Azgar901/BE_POO_KTANE/3D File/Module Timer/Erreur/Couvercle_Timer3.3mf

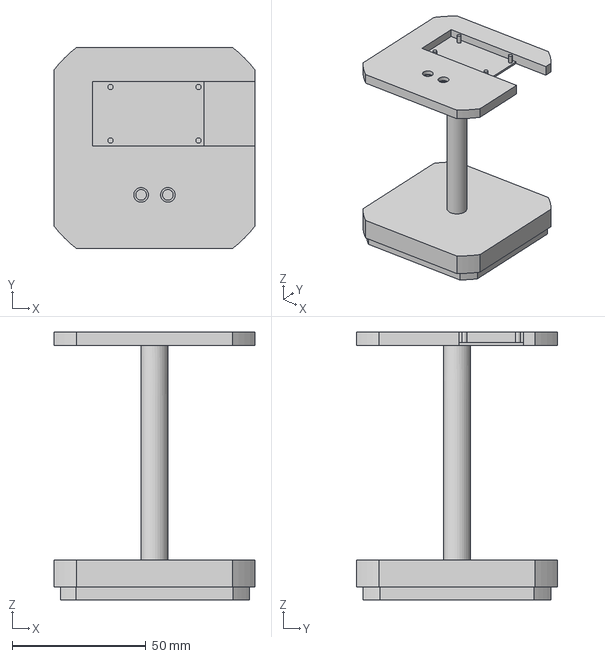
[picture p23: CAD file, 2026-01-14]
3D File/Module Timer/Erreur/Couvercle_Timer3.3mf
75.0 x 75.0 x 100.0 mm
