Azgar901/BE_POO_KTANE/3D File/Casier Modulable/Erreur/Drawer_CasingV5.3mf

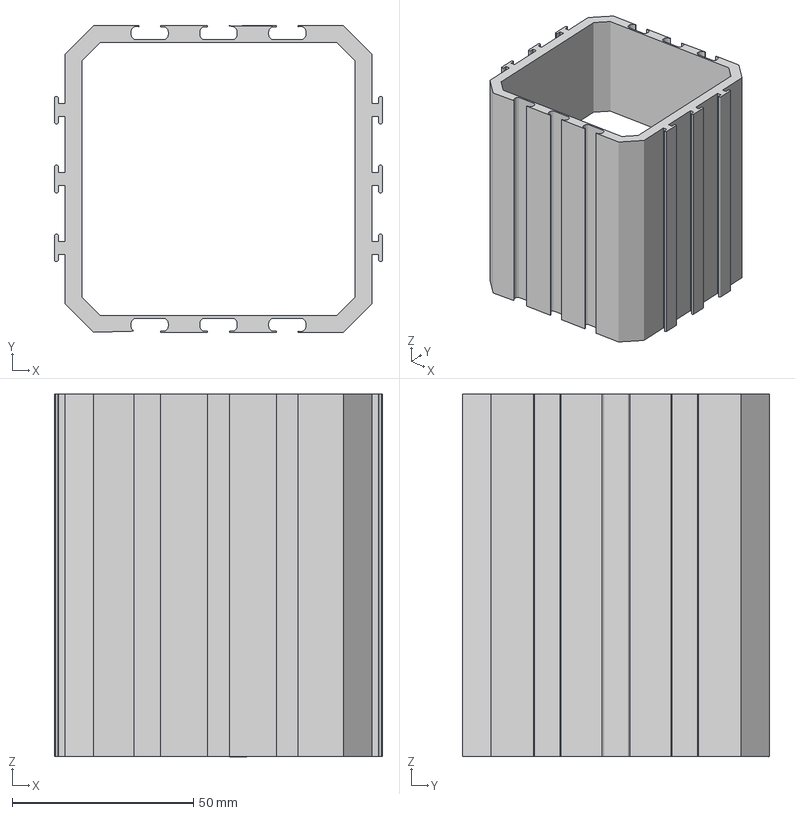
[picture p24: CAD file, 2026-01-14]
3D File/Casier Modulable/Erreur/Drawer_CasingV5.3mf
90.6 x 84.6 x 100.2 mm
