Azgar901/BE_POO_KTANE/3D File/Module LCD/Erreur/LCD_CasingV1.3mf

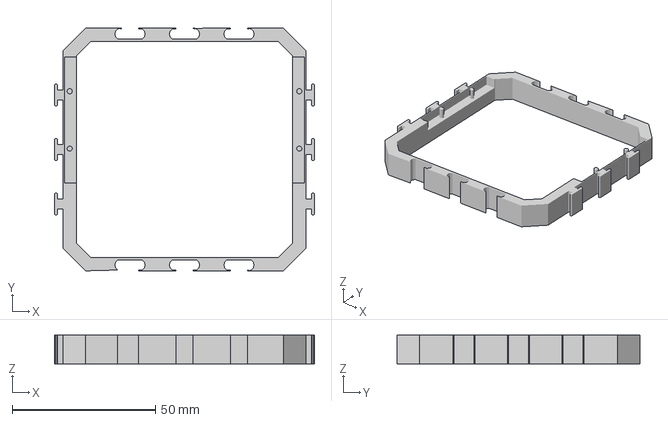
[picture p25: CAD file, 2026-01-14]
3D File/Module LCD/Erreur/LCD_CasingV1.3mf
90.6 x 84.6 x 10.0 mm
