Azgar901/BE_POO_KTANE/3D File/Module Simon/Modelisation_finale/6mm+button+PP.3mf

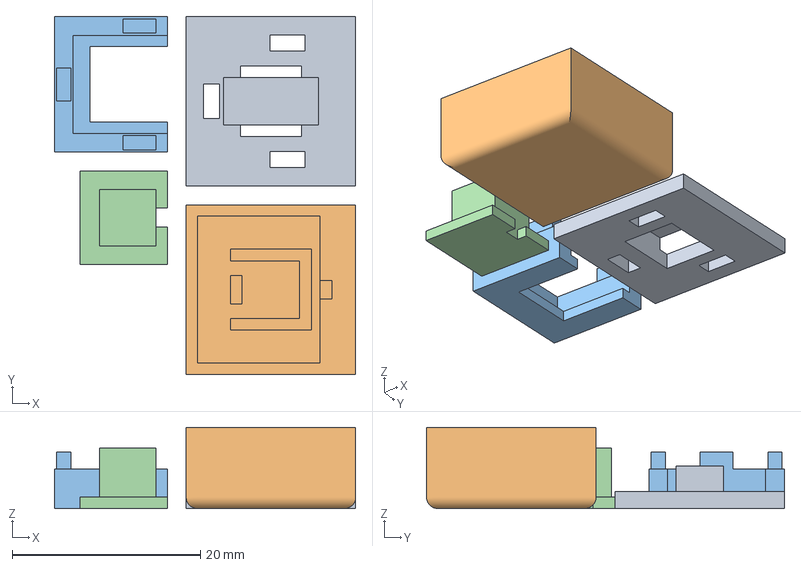
[picture p26: CAD file, 2026-01-14]
3D File/Module Simon/Modelisation_finale/6mm+button+PP.3mf
32.0 x 38.0 x 8.60 mm
