Azgar901/BE_POO_KTANE/3D File/Module Timer/Erreur/Couvercle_Timer.3mf

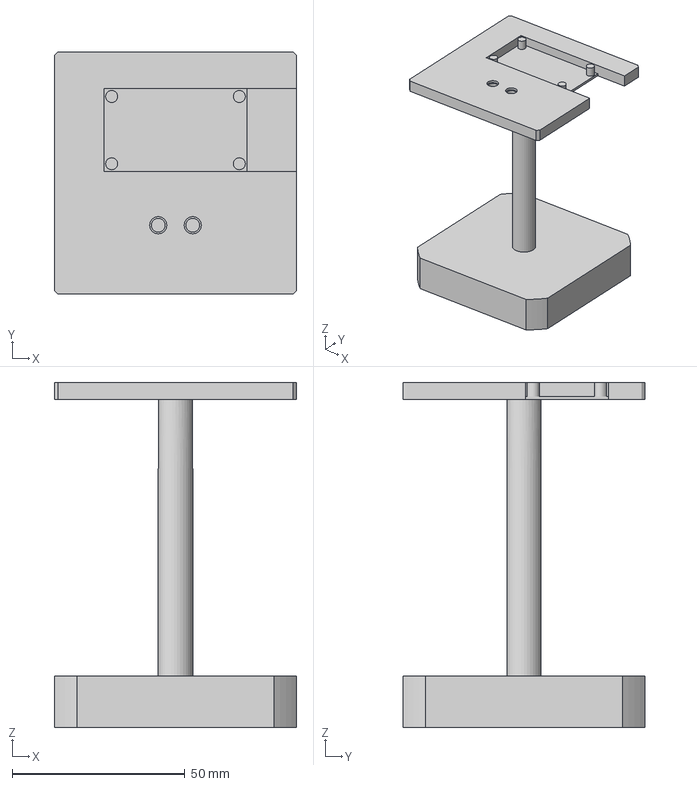
[picture p27: CAD file, 2026-01-14]
3D File/Module Timer/Erreur/Couvercle_Timer.3mf
70.3 x 70.3 x 100.0 mm
