Azgar901/BE_POO_KTANE/3D File/Module Simon/Modelisation_finale/Support Button v3.3mf

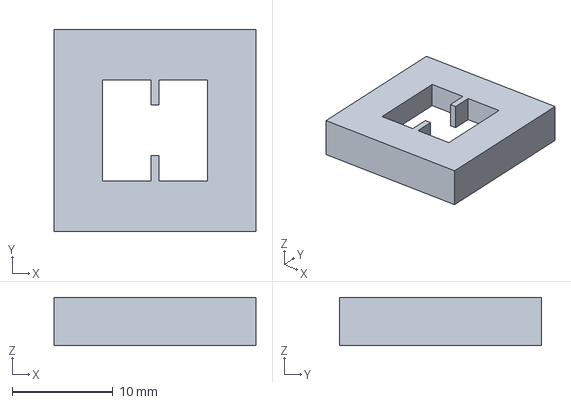
[picture p28: CAD file, 2026-01-14]
3D File/Module Simon/Modelisation_finale/Support Button v3.3mf
20.0 x 20.0 x 4.80 mm
