Azgar901/BE_POO_KTANE/3D File/Support/Erreur et tests/support3.3mf

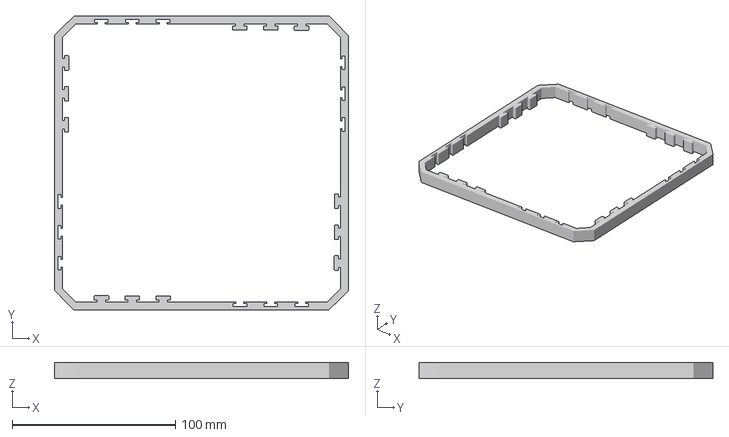
[picture p29: CAD file, 2026-01-17]
3D File/Support/Erreur et tests/support3.3mf
180.4 x 180.4 x 10.0 mm
