Azgar901/BE_POO_KTANE/Project_KTANE/Timer.hpp

//
// Created by ulric on 12/21/2025.
//

#ifndef BE_POO_KTANE_TIMER_HPP
#define BE_POO_KTANE_TIMER_HPP
#include "Bombe.hpp"

class Timer {
    int MaxTime;
    unsigned long lastUpdate;

    public:
    Timer(Bomb * b);

    void begin();
    void update(Bomb * b);
};

#endif //BE_POO_KTANE_TIMER_HPP
