Azgar901/BE_POO_KTANE/Project_KTANE/Speaker.hpp

//
// Created by ulric on 1/8/2026.
//

#ifndef BE_POO_KTANE_SPEAKER_HPP
#define BE_POO_KTANE_SPEAKER_HPP

#include "Arduino.h"

void init_Speaker();
void Play_Music(String a);

#endif //BE_POO_KTANE_SPEAKER_HPP
